Raghav67816/NID-24/images/ads.png

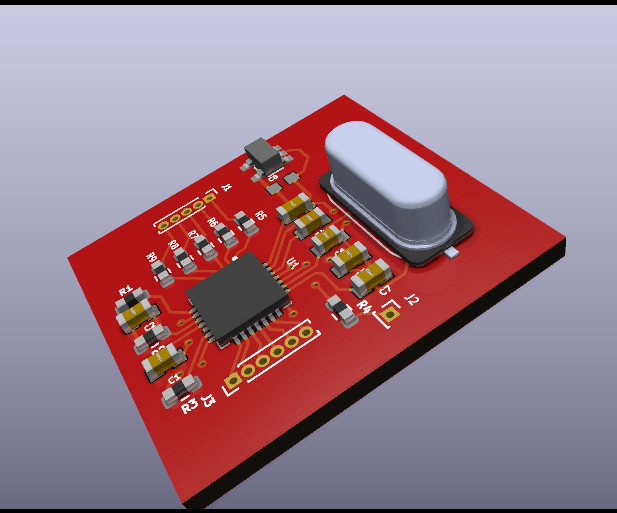
images/ads.png
