Raghav67816/NID-24/images/controller.png

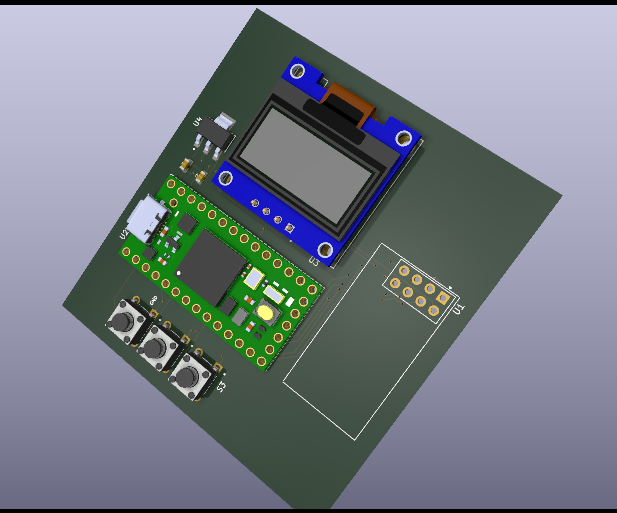
images/controller.png
