Raghav67816/NID-24/images/image-2.png

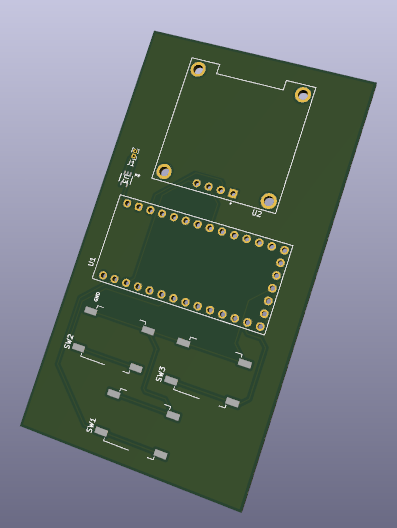
images/image-2.png
